alextechcc/fume_extractor/photos/base_mod.PNG

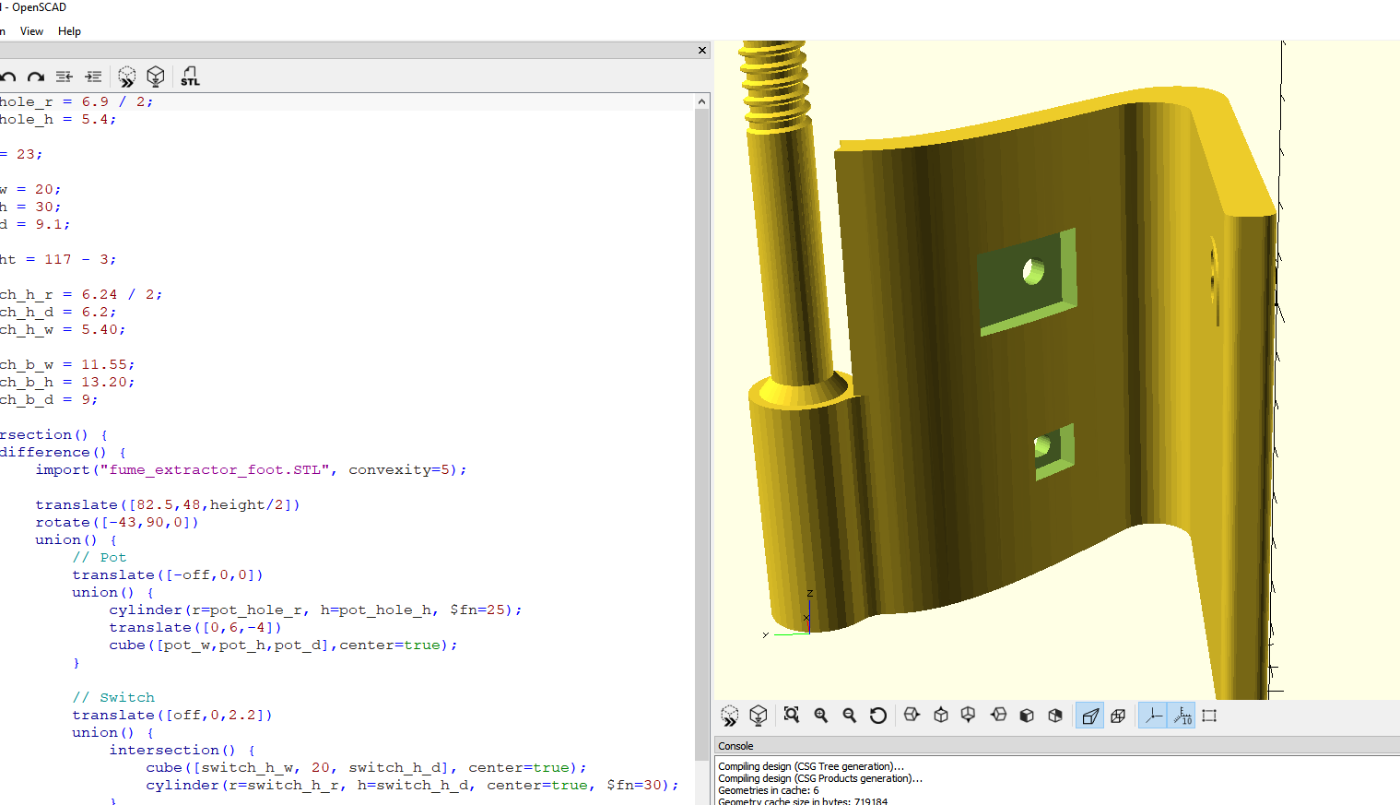
photos/base_mod.PNG
