alextechcc/fume_extractor/photos/board.PNG

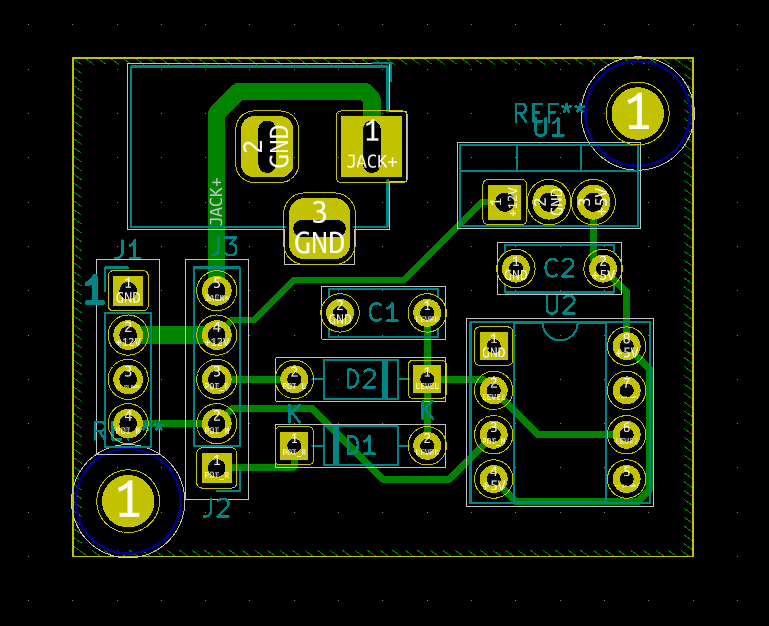
photos/board.PNG
