alextechcc/fume_extractor/photos/hookup.jpg

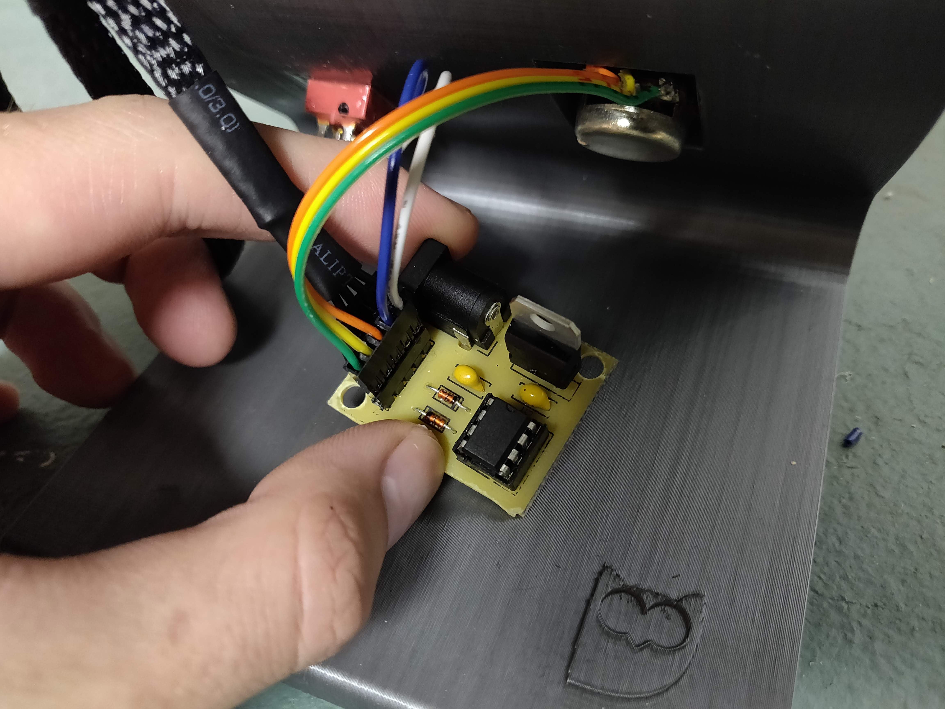
photos/hookup.jpg
