alextechcc/fume_extractor/photos/drill_setup.jpg

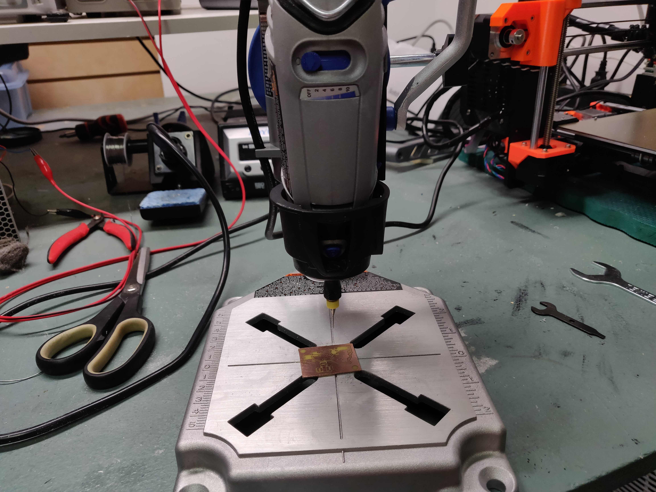
photos/drill_setup.jpg
