alextechcc/fume_extractor/photos/etched.jpg

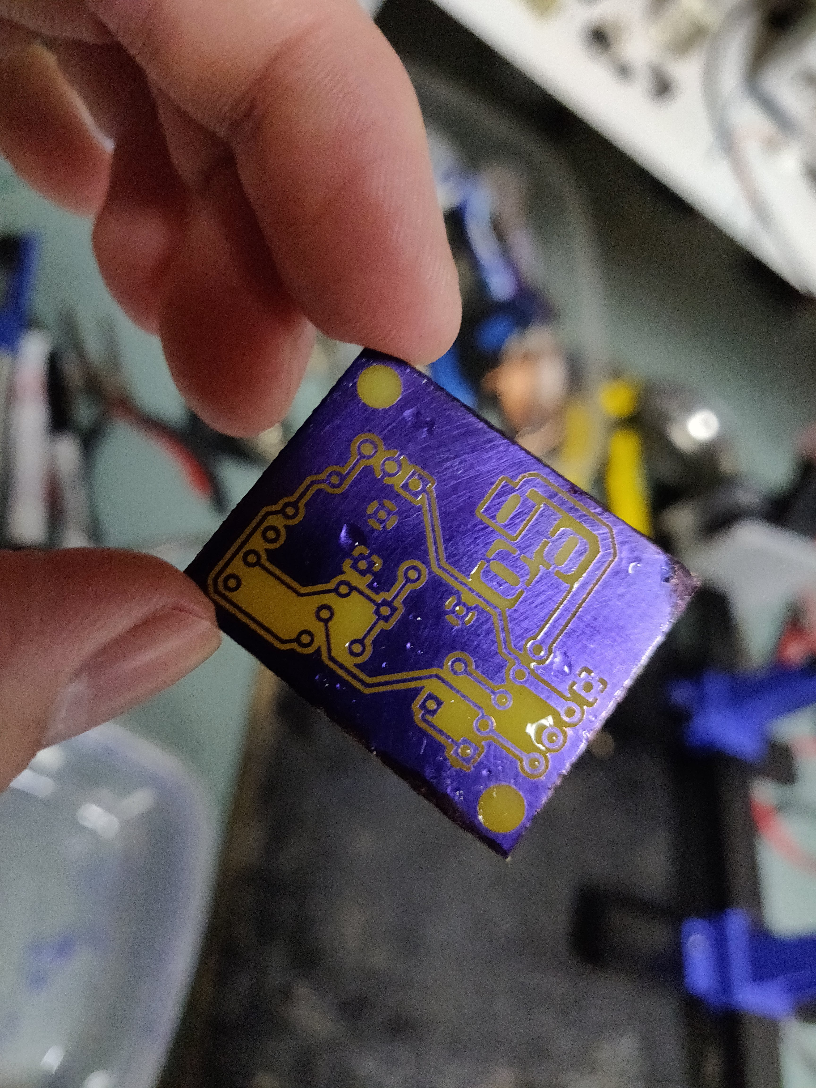
photos/etched.jpg
