alextechcc/fume_extractor/photos/exposed_developed.jpg

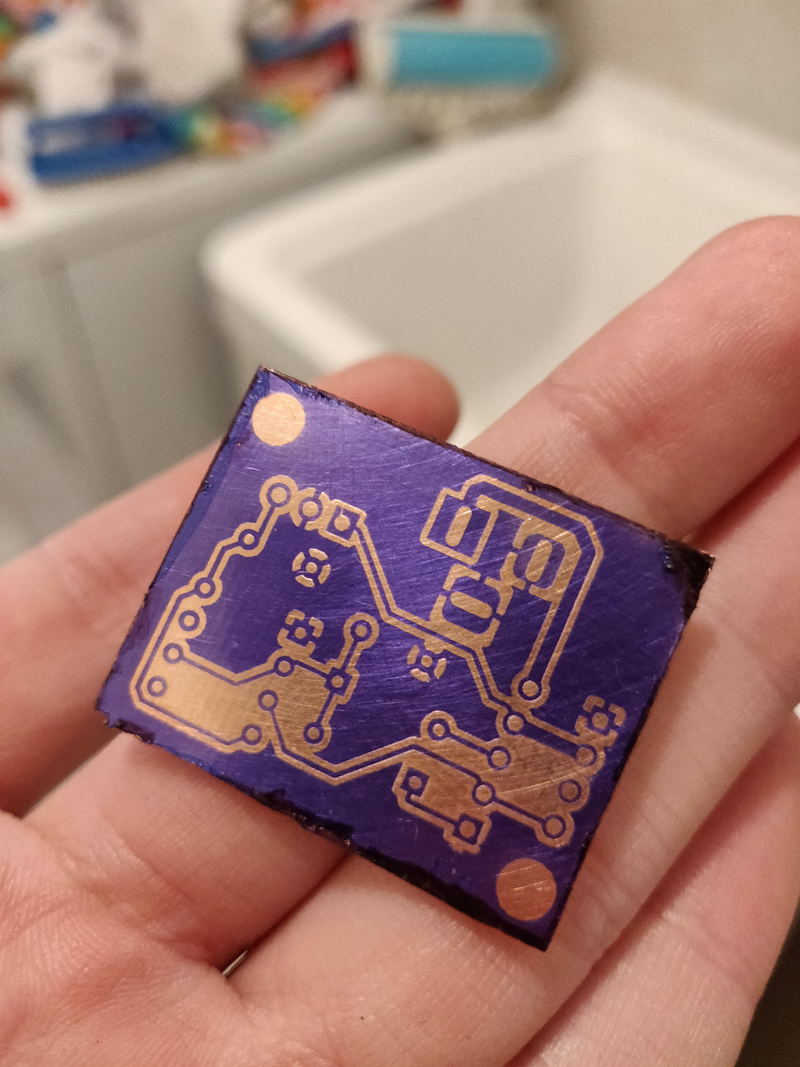
photos/exposed_developed.jpg
