alextechcc/fume_extractor/photos/silkscreen.jpg

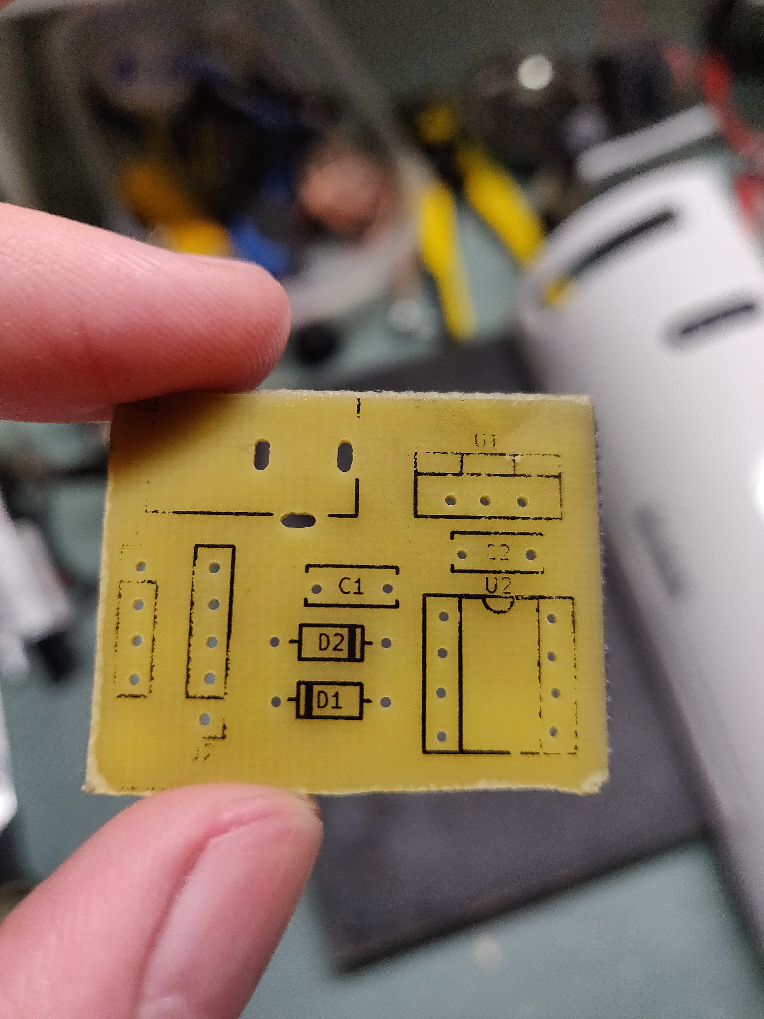
photos/silkscreen.jpg
