alextechcc/fume_extractor/photos/soldered.jpg

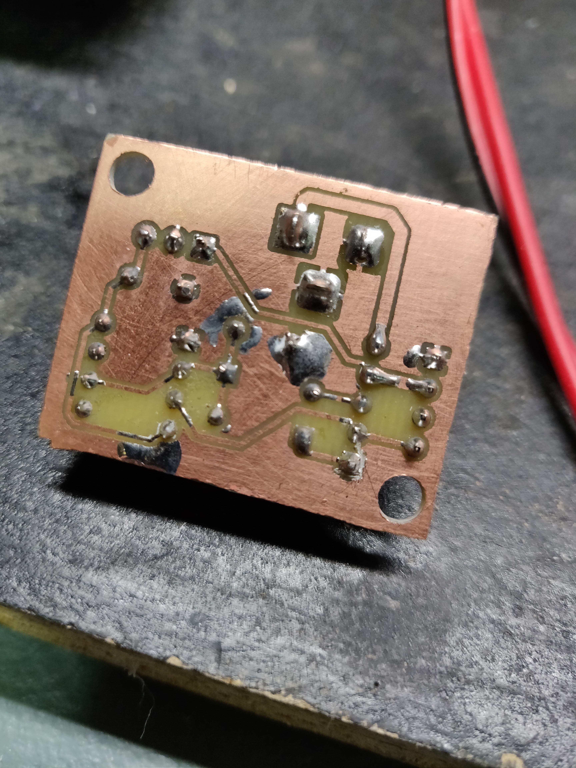
photos/soldered.jpg
